jeffqchen/miroHISCORE-3D-Mini-DIN-9-to-HD15-Adapter/KiCAD/miroHISCORE Adapter.kicad_sch

## KiCad design KiCAD/miroHISCORE Adapter.kicad_sch (2026-04-03)

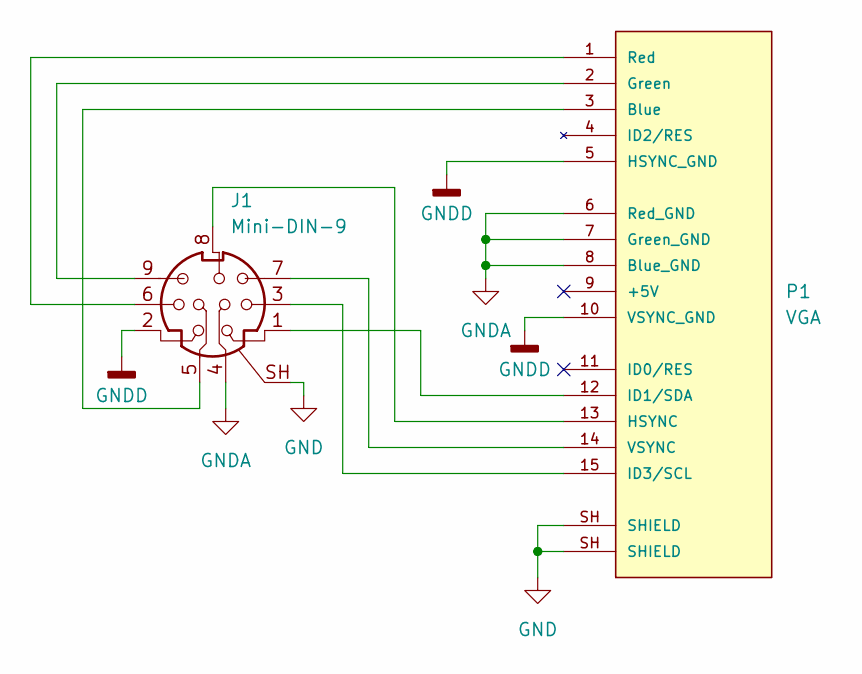
[picture p3: schematic miroHISCORE Adapter.kicad_sch]

Parts:
J1: Mini-DIN-9; 9DIN Female
P1: VGA; DSUB-15-HD_Pins_Horizontal_P2.29x2.54mm_EdgePinOffset8.35mm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; PARTREV N/A

Connections:
GND: J1.SH, P1.SH (SHIELD)
GNDA: J1.4, P1.6 (Red_GND), P1.7 (Green_GND), P1.8 (Blue_GND)
GNDD: J1.2, P1.5 (HSYNC_GND), P1.10 (VSYNC_GND)
unnamed: J1.1, P1.12 (ID1/SDA)
unnamed: J1.3, P1.15 (ID3/SCL)
unnamed: J1.5, P1.3 (Blue)
unnamed: J1.6, P1.1 (Red)
unnamed: J1.7, P1.14 (VSYNC)
unnamed: J1.8, P1.13 (HSYNC)
unnamed: J1.9, P1.2 (Green)
